MOSH-Insa-Toulouse/2023-2024-4GP-BESNARD-BRUN/Android/Face_Arriere.png

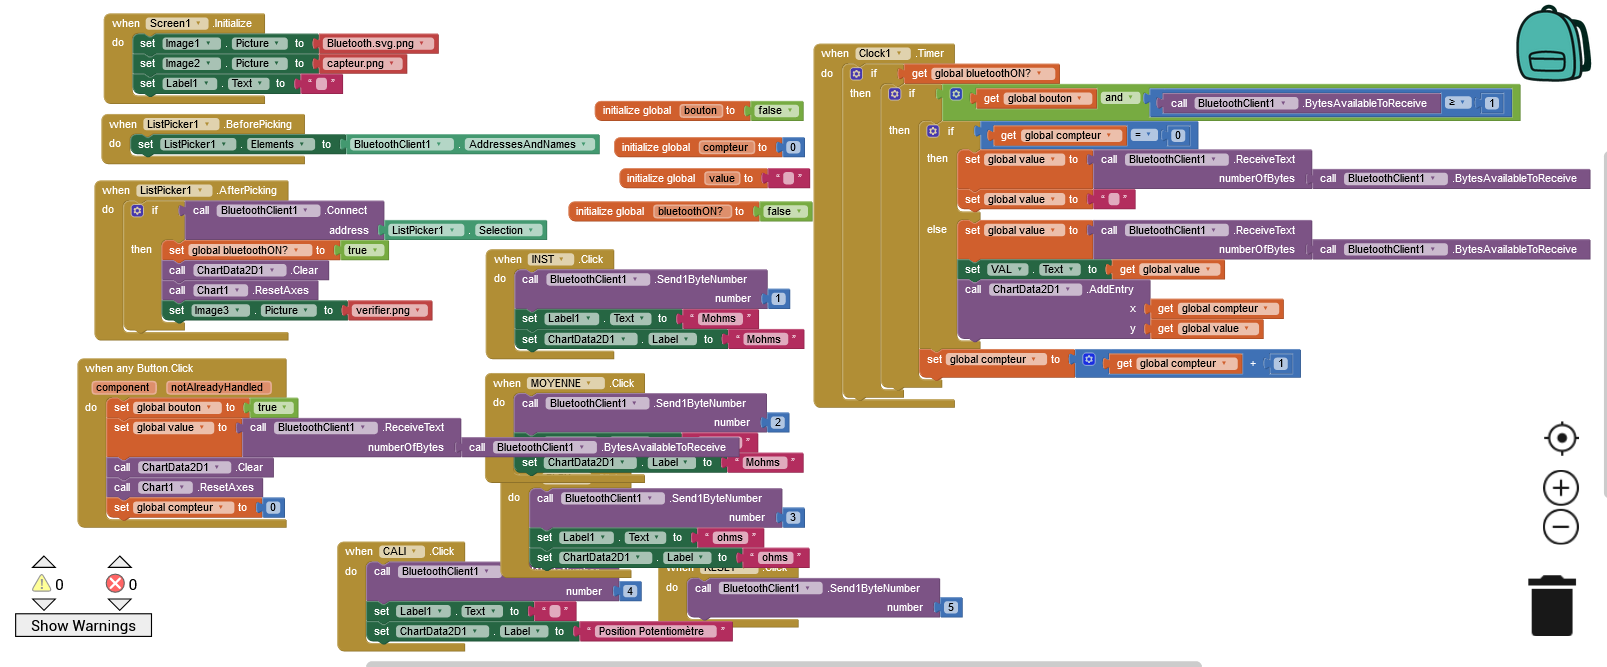
Android/Face_Arriere.png
