MOSH-Insa-Toulouse/2023-2024-4GP-BESNARD-BRUN/Android/Face_Avant_1.png

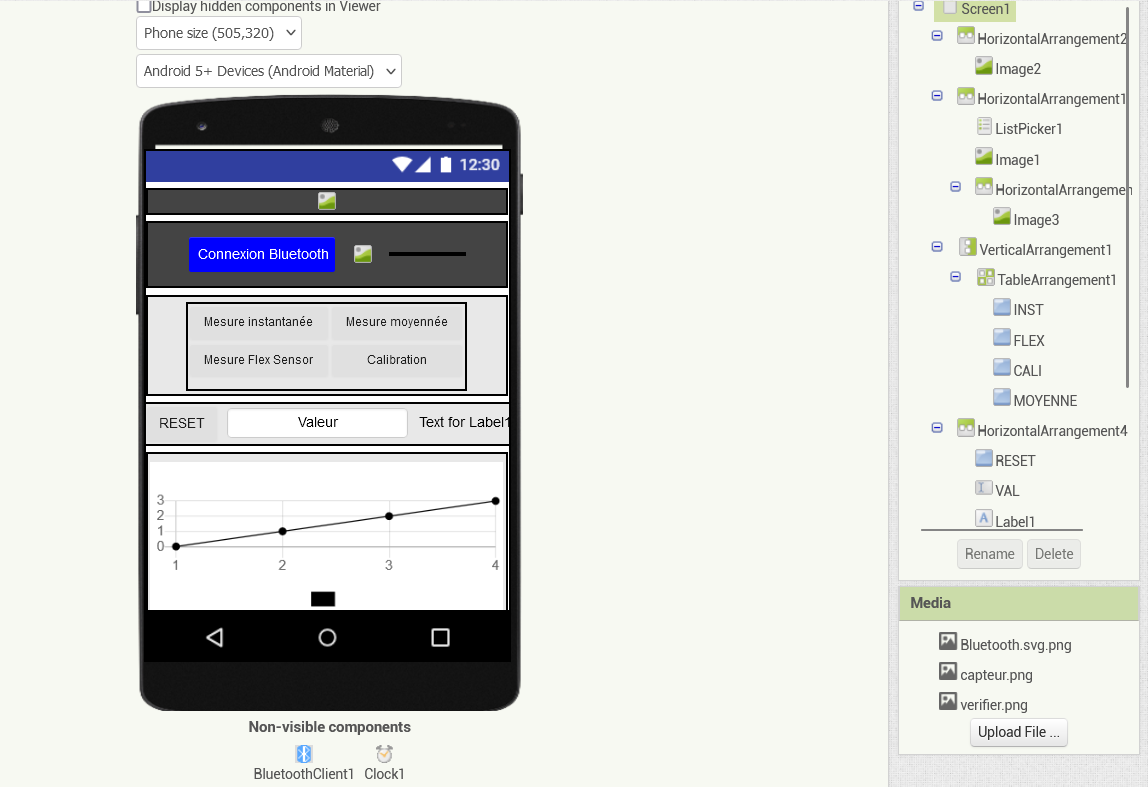
Android/Face_Avant_1.png
