MOSH-Insa-Toulouse/2023-2024-4GP-BESNARD-BRUN/Android/Face_Avant_2_liste_element.png

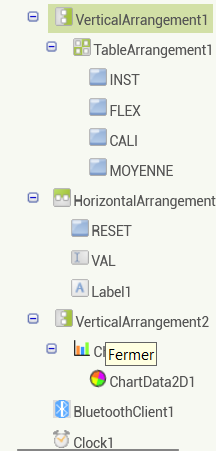
Android/Face_Avant_2_liste_element.png
